xHain-hackspace/PlotterFeeder/src/play_sound/melodies_twisst.py

# taken from https://github.com/twisst/Music-for-Raspberry-Pi-Pico under GPL-3.0

# Songs to play with a buzzer connected to a Raspberry Pi Pico.
# Ported from https://github.com/robsoncouto/arduino-songs
# 
# Contents:
#
#  0. Star Trek intro
#  1. Silent Night
#  2. Pacman
#  3. Ode an die Freude, Beethoven's Symphony No. 9
#  4. Star Wars theme
#  5. Wiegenlied (Brahms' Lullaby)
#  6. Theme A from Tetris (Korobeiniki)
#  7. Happy Birthday
#  8. Darth Vader theme (Star Wars)
#  9. Nokia Ringtone
# 10. Mii Channel theme
# 11. Minuet in G - Petzold
# 12. Badinerie - Johann Sebastian Bach
# 13. Für Elise - Ludwig van Beethoven
# 14. Cantina Band (Star wars)
# 15. Song of storms (The Legend of Zelda, Ocarina of Time)
# 16. The Lion Sleeps Tonight
# 17. The Lick
# 18. Canon in D - Pachelbel
# 19. At Doom's Gate
# 20. Pink Panther theme
# 21. Hedwig's theme (Harry Potter)
# 22. Jigglypuff's Song (Pokémon)
# 23. We Wish You a Merry Christmas
# 24. Keyboard cat
# 25. Game of Thrones
# 26. Greensleeves
# 27. Green Hill Zone (Sonic the Hedgehog)
# 28. The Legend of Zelda theme
# 29. Baby Elephant Walk
# 30. Bloody Tears (Castlevania II)
# 31. O Pulo da Gaita (Auto da Compadecida)
# 32. Vampire Killer (Castlevania)
# 33. Never Gonna Give You Up - Rick Astley
# 34. Take on me - A-ha
# 35. Prince Igor - Polovtsian Dances, Borodin
# 36. Zelda's Lullaby - The Legend of Zelda, Ocarina of Time
# 37. Super Mario Bros theme, by Koji Kondo
# 38. Asa branca - Luiz Gonzaga
# 39. The Godfather theme
# 40. Professor Layton's theme


melody = []
notes = []


# 
# Star Trek intro
# Score available at https://musescore.com/user/10768291/scores/4594271
# 
notes = ['Star Trek intro', 80, 'NOTE_D4', '-8', 'NOTE_G4', '16', 'NOTE_C5', '-4', 'NOTE_B4', '8', 'NOTE_G4', '-16', 'NOTE_E4', '-16', 'NOTE_A4', '-16', 'NOTE_D5', '2']
melody.append(notes)
# 
# Silent Night
# Score available at https://musescore.com/marcsabatella/scores/3123436
# 
notes = ['Silent Night', 140, 'NOTE_G4', '-4', 'NOTE_A4', '8', 'NOTE_G4', '4', 'NOTE_E4', '-2', 'NOTE_G4', '-4', 'NOTE_A4', '8', 'NOTE_G4', '4', 'NOTE_E4', '-2', 'NOTE_D5', '2', 'NOTE_D5', '4', 'NOTE_B4', '-2', 'NOTE_C5', '2', 'NOTE_C5', '4', 'NOTE_G4', '-2', 'NOTE_A4', '2', 'NOTE_A4', '4', 'NOTE_C5', '-4', 'NOTE_B4', '8', 'NOTE_A4', '4', 'NOTE_G4', '-4', 'NOTE_A4', '8', 'NOTE_G4', '4', 'NOTE_E4', '-2', 'NOTE_A4', '2', 'NOTE_A4', '4', 'NOTE_C5', '-4', 'NOTE_B4', '8', 'NOTE_A4', '4', 'NOTE_G4', '-4', 'NOTE_A4', '8', 'NOTE_G4', '4', 'NOTE_E4', '-2', 'NOTE_D5', '2', 'NOTE_D5', '4', 'NOTE_F5', '-4', 'NOTE_D5', '8', 'NOTE_B4', '4', 'NOTE_C5', '-2', 'NOTE_E5', '-2', 'NOTE_C5', '4', 'NOTE_G4', '4', 'NOTE_E4', '4', 'NOTE_G4', '-4', 'NOTE_F4', '8', 'NOTE_D4', '4', 'NOTE_C4', '-2', 'NOTE_C4', '-1']
melody.append(notes)
# 
# Pacman
# Score available at https://musescore.com/user/85429/scores/107109
notes = ['Pacman', 105, 'NOTE_B4', '16', 'NOTE_B5', '16', 'NOTE_FS5', '16', 'NOTE_DS5', '16', 'NOTE_B5', '32', 'NOTE_FS5', '-16', 'NOTE_DS5', '8', 'NOTE_C5', '16', 'NOTE_C6', '16', 'NOTE_G6', '16', 'NOTE_E6', '16', 'NOTE_C6', '32', 'NOTE_G6', '-16', 'NOTE_E6', '8', 'NOTE_B4', '16', 'NOTE_B5', '16', 'NOTE_FS5', '16', 'NOTE_DS5', '16', 'NOTE_B5', '32', 'NOTE_FS5', '-16', 'NOTE_DS5', '8', 'NOTE_DS5', '32', 'NOTE_E5', '32', 'NOTE_F5', '32', 'NOTE_F5', '32', 'NOTE_FS5', '32', 'NOTE_G5', '32', 'NOTE_G5', '32', 'NOTE_GS5', '32', 'NOTE_A5', '16', 'NOTE_B5', '8']
melody.append(notes)
# 
# Ode an die Freude - Beethoven's Symphony No. 9 
# 
notes = ['Ode an die Freude', 114, 'NOTE_E4', '4', 'NOTE_E4', '4', 'NOTE_F4', '4', 'NOTE_G4', '4', 'NOTE_G4', '4', 'NOTE_F4', '4', 'NOTE_E4', '4', 'NOTE_D4', '4', 'NOTE_C4', '4', 'NOTE_C4', '4', 'NOTE_D4', '4', 'NOTE_E4', '4', 'NOTE_E4', '-4', 'NOTE_D4', '8', 'NOTE_D4', '2', 'NOTE_E4', '4', 'NOTE_E4', '4', 'NOTE_F4', '4', 'NOTE_G4', '4', 'NOTE_G4', '4', 'NOTE_F4', '4', 'NOTE_E4', '4', 'NOTE_D4', '4', 'NOTE_C4', '4', 'NOTE_C4', '4', 'NOTE_D4', '4', 'NOTE_E4', '4', 'NOTE_D4', '-4', 'NOTE_C4', '8', 'NOTE_C4', '2', 'NOTE_D4', '4', 'NOTE_D4', '4', 'NOTE_E4', '4', 'NOTE_C4', '4', 'NOTE_D4', '4', 'NOTE_E4', '8', 'NOTE_F4', '8', 'NOTE_E4', '4', 'NOTE_C4', '4', 'NOTE_D4', '4', 'NOTE_E4', '8', 'NOTE_F4', '8', 'NOTE_E4', '4', 'NOTE_D4', '4', 'NOTE_C4', '4', 'NOTE_D4', '4', 'NOTE_G3', '2', 'NOTE_E4', '4', 'NOTE_E4', '4', 'NOTE_F4', '4', 'NOTE_G4', '4', 'NOTE_G4', '4', 'NOTE_F4', '4', 'NOTE_E4', '4', 'NOTE_D4', '4', 'NOTE_C4', '4', 'NOTE_C4', '4', 'NOTE_D4', '4', 'NOTE_E4', '4', 'NOTE_D4', '-4', 'NOTE_C4', '8', 'NOTE_C4', '2']
melody.append(notes)
# 
# Star Wars theme
#
notes = ['Star Wars theme', 108, 'NOTE_AS4', '8', 'NOTE_AS4', '8', 'NOTE_AS4', '8', 'NOTE_F5', '2', 'NOTE_C6', '2', 'NOTE_AS5', '8', 'NOTE_A5', '8', 'NOTE_G5', '8', 'NOTE_F6', '2', 'NOTE_C6', '4', 'NOTE_AS5', '8', 'NOTE_A5', '8', 'NOTE_G5', '8', 'NOTE_F6', '2', 'NOTE_C6', '4', 'NOTE_AS5', '8', 'NOTE_A5', '8', 'NOTE_AS5', '8', 'NOTE_G5', '2', 'NOTE_C5', '8', 'NOTE_C5', '8', 'NOTE_C5', '8', 'NOTE_F5', '2', 'NOTE_C6', '2', 'NOTE_AS5', '8', 'NOTE_A5', '8', 'NOTE_G5', '8', 'NOTE_F6', '2', 'NOTE_C6', '4', 'NOTE_AS5', '8', 'NOTE_A5', '8', 'NOTE_G5', '8', 'NOTE_F6', '2', 'NOTE_C6', '4', 'NOTE_AS5', '8', 'NOTE_A5', '8', 'NOTE_AS5', '8', 'NOTE_G5', '2', 'NOTE_C5', '-8', 'NOTE_C5', '16', 'NOTE_D5', '-4', 'NOTE_D5', '8', 'NOTE_AS5', '8', 'NOTE_A5', '8', 'NOTE_G5', '8', 'NOTE_F5', '8', 'NOTE_F5', '8', 'NOTE_G5', '8', 'NOTE_A5', '8', 'NOTE_G5', '4', 'NOTE_D5', '8', 'NOTE_E5', '4', 'NOTE_C5', '-8', 'NOTE_C5', '16', 'NOTE_D5', '-4', 'NOTE_D5', '8', 'NOTE_AS5', '8', 'NOTE_A5', '8', 'NOTE_G5', '8', 'NOTE_F5', '8', 'NOTE_C6', '-8', 'NOTE_G5', '16', 'NOTE_G5', '2', 'REST', '8', 'NOTE_C5', '8', 'NOTE_D5', '-4', 'NOTE_D5', '8', 'NOTE_AS5', '8', 'NOTE_A5', '8', 'NOTE_G5', '8', 'NOTE_F5', '8', 'NOTE_F5', '8', 'NOTE_G5', '8', 'NOTE_A5', '8', 'NOTE_G5', '4', 'NOTE_D5', '8', 'NOTE_E5', '4', 'NOTE_C6', '-8', 'NOTE_C6', '16', 'NOTE_F6', '4', 'NOTE_DS6', '8', 'NOTE_CS6', '4', 'NOTE_C6', '8', 'NOTE_AS5', '4', 'NOTE_GS5', '8', 'NOTE_G5', '4', 'NOTE_F5', '8', 'NOTE_C6', '1']
melody.append(notes)
# 
# Wiegenlied (Brahms' Lullaby)
# Score available at https://www.flutetunes.com/tunes.php?id=54
# 
notes = ['Wiegenlied (Brahms\' Lullaby)', 76, 'NOTE_G4', '4', 'NOTE_G4', '4', 'NOTE_AS4', '-4', 'NOTE_G4', '8', 'NOTE_G4', '4', 'NOTE_AS4', '4', 'REST', '4', 'NOTE_G4', '8', 'NOTE_AS4', '8', 'NOTE_DS5', '4', 'NOTE_D5', '-4', 'NOTE_C5', '8', 'NOTE_C5', '4', 'NOTE_AS4', '4', 'NOTE_F4', '8', 'NOTE_G4', '8', 'NOTE_GS4', '4', 'NOTE_F4', '4', 'NOTE_F4', '8', 'NOTE_G4', '8', 'NOTE_GS4', '4', 'REST', '4', 'NOTE_F4', '8', 'NOTE_GS4', '8', 'NOTE_D5', '8', 'NOTE_C5', '8', 'NOTE_AS4', '4', 'NOTE_D5', '4', 'NOTE_DS5', '4', 'REST', '4', 'NOTE_DS4', '8', 'NOTE_DS4', '8', 'NOTE_DS5', '2', 'NOTE_C5', '8', 'NOTE_GS4', '8', 'NOTE_AS4', '2', 'NOTE_G4', '8', 'NOTE_DS4', '8', 'NOTE_GS4', '4', 'NOTE_AS4', '4', 'NOTE_C5', '4', 'NOTE_AS4', '2', 'NOTE_DS4', '8', 'NOTE_DS4', '8', 'NOTE_DS5', '2', 'NOTE_C5', '8', 'NOTE_GS4', '8', 'NOTE_AS4', '2', 'NOTE_G4', '8', 'NOTE_DS4', '8', 'NOTE_AS4', '4', 'NOTE_G4', '4', 'NOTE_DS4', '4', 'NOTE_DS4', '2']
melody.append(notes)
# 
# Theme A from Tetris (Korobeiniki)
# Based on the arrangement at https://www.flutetunes.com/tunes.php?id=192
# 
notes = ['Theme A from Tetris (Korobeiniki)', 144, 'NOTE_E5', '4', 'NOTE_B4', '8', 'NOTE_C5', '8', 'NOTE_D5', '4', 'NOTE_C5', '8', 'NOTE_B4', '8', 'NOTE_A4', '4', 'NOTE_A4', '8', 'NOTE_C5', '8', 'NOTE_E5', '4', 'NOTE_D5', '8', 'NOTE_C5', '8', 'NOTE_B4', '-4', 'NOTE_C5', '8', 'NOTE_D5', '4', 'NOTE_E5', '4', 'NOTE_C5', '4', 'NOTE_A4', '4', 'NOTE_A4', '8', 'NOTE_A4', '4', 'NOTE_B4', '8', 'NOTE_C5', '8', 'NOTE_D5', '-4', 'NOTE_F5', '8', 'NOTE_A5', '4', 'NOTE_G5', '8', 'NOTE_F5', '8', 'NOTE_E5', '-4', 'NOTE_C5', '8', 'NOTE_E5', '4', 'NOTE_D5', '8', 'NOTE_C5', '8', 'NOTE_B4', '4', 'NOTE_B4', '8', 'NOTE_C5', '8', 'NOTE_D5', '4', 'NOTE_E5', '4', 'NOTE_C5', '4', 'NOTE_A4', '4', 'NOTE_A4', '4', 'REST', '4', 'NOTE_E5', '4', 'NOTE_B4', '8', 'NOTE_C5', '8', 'NOTE_D5', '4', 'NOTE_C5', '8', 'NOTE_B4', '8', 'NOTE_A4', '4', 'NOTE_A4', '8', 'NOTE_C5', '8', 'NOTE_E5', '4', 'NOTE_D5', '8', 'NOTE_C5', '8', 'NOTE_B4', '-4', 'NOTE_C5', '8', 'NOTE_D5', '4', 'NOTE_E5', '4', 'NOTE_C5', '4', 'NOTE_A4', '4', 'NOTE_A4', '8', 'NOTE_A4', '4', 'NOTE_B4', '8', 'NOTE_C5', '8', 'NOTE_D5', '-4', 'NOTE_F5', '8', 'NOTE_A5', '4', 'NOTE_G5', '8', 'NOTE_F5', '8', 'NOTE_E5', '-4', 'NOTE_C5', '8', 'NOTE_E5', '4', 'NOTE_D5', '8', 'NOTE_C5', '8', 'NOTE_B4', '4', 'NOTE_B4', '8', 'NOTE_C5', '8', 'NOTE_D5', '4', 'NOTE_E5', '4', 'NOTE_C5', '4', 'NOTE_A4', '4', 'NOTE_A4', '4', 'REST', '4', 'NOTE_E5', '2', 'NOTE_C5', '2', 'NOTE_D5', '2', 'NOTE_B4', '2', 'NOTE_C5', '2', 'NOTE_A4', '2', 'NOTE_GS4', '2', 'NOTE_B4', '4', 'REST', '8', 'NOTE_E5', '2', 'NOTE_C5', '2', 'NOTE_D5', '2', 'NOTE_B4', '2', 'NOTE_C5', '4', 'NOTE_E5', '4', 'NOTE_A5', '2', 'NOTE_GS5', '2']
melody.append(notes)
# 
# Happy Birthday
# Score available at https://musescore.com/user/8221/scores/26906
# 
notes = ['Happy Birthday', 140, 'NOTE_C4', '4', 'NOTE_C4', '8', 'NOTE_D4', '-4', 'NOTE_C4', '-4', 'NOTE_F4', '-4', 'NOTE_E4', '-2', 'NOTE_C4', '4', 'NOTE_C4', '8', 'NOTE_D4', '-4', 'NOTE_C4', '-4', 'NOTE_G4', '-4', 'NOTE_F4', '-2', 'NOTE_C4', '4', 'NOTE_C4', '8', 'NOTE_C5', '-4', 'NOTE_A4', '-4', 'NOTE_F4', '-4', 'NOTE_E4', '-4', 'NOTE_D4', '-4', 'NOTE_AS4', '4', 'NOTE_AS4', '8', 'NOTE_A4', '-4', 'NOTE_F4', '-4', 'NOTE_G4', '-4', 'NOTE_F4', '-2']
melody.append(notes)
# 
# Darth Vader theme (Imperial March) - Star wars
# Score available at https://musescore.com/user/202909/scores/1141521
# The tenor saxophone part was used
# 
notes = ['Dart Vader theme', 120, 'NOTE_A4', '-4', 'NOTE_A4', '-4', 'NOTE_A4', '16', 'NOTE_A4', '16', 'NOTE_A4', '16', 'NOTE_A4', '16', 'NOTE_F4', '8', 'REST', '8', 'NOTE_A4', '-4', 'NOTE_A4', '-4', 'NOTE_A4', '16', 'NOTE_A4', '16', 'NOTE_A4', '16', 'NOTE_A4', '16', 'NOTE_F4', '8', 'REST', '8', 'NOTE_A4', '4', 'NOTE_A4', '4', 'NOTE_A4', '4', 'NOTE_F4', '-8', 'NOTE_C5', '16', 'NOTE_A4', '4', 'NOTE_F4', '-8', 'NOTE_C5', '16', 'NOTE_A4', '2', 'NOTE_E5', '4', 'NOTE_E5', '4', 'NOTE_E5', '4', 'NOTE_F5', '-8', 'NOTE_C5', '16', 'NOTE_A4', '4', 'NOTE_F4', '-8', 'NOTE_C5', '16', 'NOTE_A4', '2', 'NOTE_A5', '4', 'NOTE_A4', '-8', 'NOTE_A4', '16', 'NOTE_A5', '4', 'NOTE_GS5', '-8', 'NOTE_G5', '16', 'NOTE_DS5', '16', 'NOTE_D5', '16', 'NOTE_DS5', '8', 'REST', '8', 'NOTE_A4', '8', 'NOTE_DS5', '4', 'NOTE_D5', '-8', 'NOTE_CS5', '16', 'NOTE_C5', '16', 'NOTE_B4', '16', 'NOTE_C5', '16', 'REST', '8', 'NOTE_F4', '8', 'NOTE_GS4', '4', 'NOTE_F4', '-8', 'NOTE_A4', '-16', 'NOTE_C5', '4', 'NOTE_A4', '-8', 'NOTE_C5', '16', 'NOTE_E5', '2', 'NOTE_A5', '4', 'NOTE_A4', '-8', 'NOTE_A4', '16', 'NOTE_A5', '4', 'NOTE_GS5', '-8', 'NOTE_G5', '16', 'NOTE_DS5', '16', 'NOTE_D5', '16', 'NOTE_DS5', '8', 'REST', '8', 'NOTE_A4', '8', 'NOTE_DS5', '4', 'NOTE_D5', '-8', 'NOTE_CS5', '16', 'NOTE_C5', '16', 'NOTE_B4', '16', 'NOTE_C5', '16', 'REST', '8', 'NOTE_F4', '8', 'NOTE_GS4', '4', 'NOTE_F4', '-8', 'NOTE_A4', '-16', 'NOTE_A4', '4', 'NOTE_F4', '-8', 'NOTE_C5', '16', 'NOTE_A4', '2']
melody.append(notes)
# 
# Nokia Ringtone
# Score available at https://musescore.com/user/29944637/scores/5266155
# 
notes = ['Nokia Ringtone', 180, 'NOTE_E5', '8', 'NOTE_D5', '8', 'NOTE_FS4', '4', 'NOTE_GS4', '4', 'NOTE_CS5', '8', 'NOTE_B4', '8', 'NOTE_D4', '4', 'NOTE_E4', '4', 'NOTE_B4', '8', 'NOTE_A4', '8', 'NOTE_CS4', '4', 'NOTE_E4', '4', 'NOTE_A4', '2']
melody.append(notes)
# 
# Mii Channel theme
# Score available at https://musescore.com/user/16403456/scores/4984153
# 
notes = ['Mii Channel theme', 114, 'NOTE_FS4', '8', 'REST', '8', 'NOTE_A4', '8', 'NOTE_CS5', '8', 'REST', '8', 'NOTE_A4', '8', 'REST', '8', 'NOTE_FS4', '8', 'NOTE_D4', '8', 'NOTE_D4', '8', 'NOTE_D4', '8', 'REST', '8', 'REST', '4', 'REST', '8', 'NOTE_CS4', '8', 'NOTE_D4', '8', 'NOTE_FS4', '8', 'NOTE_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
melody.append(notes)
# 
# Minuet in G - Petzold
# Score available at https://musescore.com/user/3402766/scores/1456391
notes = ['Minuet in G - Petzold', 140, 'NOTE_D5', '4', 'NOTE_G4', '8', 'NOTE_A4', '8', 'NOTE_B4', '8', 'NOTE_C5', '8', 'NOTE_D5', '4', 'NOTE_G4', '4', 'NOTE_G4', '4', 'NOTE_E5', '4', 'NOTE_C5', '8', 'NOTE_D5', '8', 'NOTE_E5', '8', 'NOTE_FS5', '8', 'NOTE_G5', '4', 'NOTE_G4', '4', 'NOTE_G4', '4', 'NOT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
melody.append(notes)
#
# Badinerie - Johann Sebastian Bach
notes = ['Badinerie - Johann Sebastian Bach', 120, 'NOTE_B5', '-8', 'NOTE_D6', '16', 'NOTE_B5', '16', 'NOTE_FS5', '-8', 'NOTE_B5', '16', 'NOTE_FS5', '16', 'NOTE_D5', '-8', 'NOTE_FS5', '16', 'NOTE_D5', '16', 'NOTE_B4', '4', 'NOTE_F4', '16', 'NOTE_B4', '16', 'NOTE_D5', '16', 'NOTE_B4', '16', 'NOTE_CS5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
melody.append(notes)
# 
# Für Elise - Ludwig van Beethoven
# Score available at https://musescore.com/user/28149610/scores/5281944
# 
notes = ['Für Elise - Ludwig van Beethoven', 80, 'NOTE_E5', '16', 'NOTE_DS5', '16', 'NOTE_E5', '16', 'NOTE_DS5', '16', 'NOTE_E5', '16', 'NOTE_B4', '16', 'NOTE_D5', '16', 'NOTE_C5', '16', 'NOTE_A4', '-8', 'NOTE_C4', '16', 'NOTE_E4', '16', 'NOTE_A4', '16', 'NOTE_B4', '-8', 'NOTE_E4', '16', 'NOTE_GS4', '16', 'NOTE_B4', '16', 'NOTE_C5', '8', 'REST', '16', 'NOTE_E4', '16', 'NOTE_E5', '16', 'NOTE_DS5', '16', 'NOTE_E5', '16', 'NOTE_DS5', '16', 'NOTE_E5', '16', 'NOTE_B4', '16', 'NOTE_D5', '16', 'NOTE_C5', '16', 'NOTE_A4', '-8', 'NOTE_C4', '16', 'NOTE_E4', '16', 'NOTE_A4', '16', 'NOTE_B4', '-8', 'NOTE_E4', '16', 'NOTE_C5', '16', 'NOTE_B4', '16', 'NOTE_A4', '4', 'REST', '8', 'NOTE_E5', '16', 'NOTE_DS5', '16', 'NOTE_E5', '16', 'NOTE_DS5', '16', 'NOTE_E5', '16', 'NOTE_B4', '16', 'NOTE_D5', '16', 'NOTE_C5', '16', 'NOTE_A4', '-8', 'NOTE_C4', '16', 'NOTE_E4', '16', 'NOTE_A4', '16', 'NOTE_B4', '-8', 'NOTE_E4', '16', 'NOTE_GS4', '16', 'NOTE_B4', '16', 'NOTE_C5', '8', 'REST', '16', 'NOTE_E4', '16', 'NOTE_E5', '16', 'NOTE_DS5', '16', 'NOTE_E5', '16', 'NOTE_DS5', '16', 'NOTE_E5', '16', 'NOTE_B4', '16', 'NOTE_D5', '16', 'NOTE_C5', '16', 'NOTE_A4', '-8', 'NOTE_C4', '16', 'NOTE_E4', '16', 'NOTE_A4', '16', 'NOTE_B4', '-8', 'NOTE_E4', '16', 'NOTE_C5', '16', 'NOTE_B4', '16', 'NOTE_A4', '8', 'REST', '16', 'NOTE_B4', '16', 'NOTE_C5', '16', 'NOTE_D5', '16', 'NOTE_E5', '-8', 'NOTE_G4', '16', 'NOTE_F5', '16', 'NOTE_E5', '16', 'NOTE_D5', '-8', 'NOTE_F4', '16', 'NOTE_E5', '16', 'NOTE_D5', '16', 'NOTE_C5', '-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
6', 'NOTE_B4', '16', 'NOTE_D5', '16', 'NOTE_C5', '16', 'NOTE_A4', '-8', 'NOTE_C4', '16', 'NOTE_E4', '16', 'NOTE_A4', '16', 'NOTE_B4', '-8', 'NOTE_E4', '16', 'NOTE_C5', '16', 'NOTE_B4', '16', 'NOTE_A4', '-8', 'REST', '-8', 'REST', '-8', 'NOTE_G4', '16', 'NOTE_F5', '16', 'NOTE_E5', '16', 'NOTE_D5', '4', 'REST', '8', 'REST', '-8', 'NOTE_E4', '16', 'NOTE_D5', '16', 'NOTE_C5', '16', 'NOTE_B4', '-8', 'NOTE_E4', '16', 'NOTE_E5', '8', 'NOTE_E5', '8', 'NOTE_E6', '-8', 'NOTE_DS5', '16', 'NOTE_E5', '16', 'REST', '16', 'REST', '16', 'NOTE_DS5', '16', 'NOTE_E5', '16', 'NOTE_DS5', '16', 'NOTE_E5', '16', 'NOTE_DS5', '16', 'NOTE_E5', '16', 'NOTE_B4', '16', 'NOTE_D5', '16', 'NOTE_C5', '16', 'NOTE_A4', '-8', 'NOTE_C4', '16', 'NOTE_E4', '16', 'NOTE_A4', '16', 'NOTE_B4', '-8', 'NOTE_E4', '16', 'NOTE_GS4', '16', 'NOTE_B4', '16', 'NOTE_C5', '8', 'REST', '16', 'NOTE_E4', '16', 'NOTE_E5', '16', 'NOTE_DS5', '16', 'NOTE_E5', '16', 'NOTE_DS5', '16', 'NOTE_E5', '16', 'NOTE_B4', '16', 'NOTE_D5', '16', 'NOTE_C5', '16', 'NOTE_A4', '-8', 'NOTE_C4', '16', 'NOTE_E4', '16', 'NOTE_A4', '16', 'NOTE_B4', '-8', 'NOTE_E4', '16', 'NOTE_C5', '16', 'NOTE_B4', '16', 'NOTE_A4', '-4']
melody.append(notes)
# 
# Cantina Band (Star wars)
# Score available at https://musescore.com/user/6795541/scores/1606876
notes = ['Cantina Band (Star wars)', 140, 'NOTE_B4', '-4', 'NOTE_E5', '-4', 'NOTE_B4', '-4', 'NOTE_E5', '-4', 'NOTE_B4', '8', 'NOTE_E5', '-4', 'NOTE_B4', '8', 'REST', '8', 'NOTE_AS4', '8', 'NOTE_B4', '8', 'NOTE_B4', '8', 'NOTE_AS4', '8', 'NOTE_B4', '8', 'NOTE_A4', '8', 'REST', '8', 'NOTE_GS4', '8', 'NOTE_A4', '8', 'NOTE_G4', '8', 'NOTE_G4', '4', 'NOTE_E4', '-2', 'NOTE_B4', '-4', 'NOTE_E5', '-4', 'NOTE_B4', '-4', 'NOTE_E5', '-4', 'NOTE_B4', '8', 'NOTE_E5', '-4', 'NOTE_B4', '8', 'REST', '8', 'NOTE_AS4', '8', 'NOTE_B4', '8', 'NOTE_A4', '-4', 'NOTE_A4', '-4', 'NOTE_GS4', '8', 'NOTE_A4', '-4', 'NOTE_D5', '8', 'NOTE_C5', '-4', 'NOTE_B4', '-4', 'NOTE_A4', '-4', 'NOTE_B4', '-4', 'NOTE_E5', '-4', 'NOTE_B4', '-4', 'NOTE_E5', '-4', 'NOTE_B4', '8', 'NOTE_E5', '-4', 'NOTE_B4', '8', 'REST', '8', 'NOTE_AS4', '8', 'NOTE_B4', '8', 'NOTE_D5', '4', 'NOTE_D5', '-4', 'NOTE_B4', '8', 'NOTE_A4', '-4', 'NOTE_G4', '-4', 'NOTE_E4', '-2', 'NOTE_E4', '2', 'NOTE_G4', '2', 'NOTE_B4', '2', 'NOTE_D5', '2', 'NOTE_F5', '-4', 'NOTE_E5', '-4', 'NOTE_AS4', '8', 'NOTE_AS4', '8', 'NOTE_B4', '4', 'NOTE_G4', '4']
melody.append(notes)
# 
# Song of storms (The Legend of Zelda, Ocarina of Time)
# Score available at https://musescore.com/user/4957541/scores/1545401
# 
notes = ['Song of storms (The Legend of Zelda, Ocarina of Time)', 108, 'NOTE_D4', '4', 'NOTE_A4', '4', 'NOTE_A4', '4', 'REST', '8', 'NOTE_E4', '8', 'NOTE_B4', '2', 'NOTE_F4', '4', 'NOTE_C5', '4', 'NOTE_C5', '4', 'REST', '8', 'NOTE_E4', '8', 'NOTE_B4', '2', 'NOTE_D4', '4', 'NOTE_A4', '4', 'NOTE_A4', '4', 'REST', '8', 'NOTE_E4', '8', 'NOTE_B4', '2', 'NOTE_F4', '4', 'NOTE_C5', '4', 'NOTE_C5', '4', 'REST', '8', 'NOTE_E4', '8', 'NOTE_B4', '2', 'NOTE_D4', '8', 'NOTE_F4', '8', 'NOTE_D5', '2', 'NOTE_D4', '8', 'NOTE_F4', '8', 'NOTE_D5', '2', 'NOTE_E5', '-4', 'NOTE_F5', '8', 'NOTE_E5', '8', 'NOTE_E5', '8', 'NOTE_E5', '8', 'NOTE_C5', '8', 'NOTE_A4', '2', 'NOTE_A4', '4', 'NOTE_D4', '4', 'NOTE_F4', '8', 'NOTE_G4', '8', 'NOTE_A4', '-2', 'NOTE_A4', '4', 'NOTE_D4', '4', 'NOTE_F4', '8', 'NOTE_G4', '8', 'NOTE_E4', '-2', 'NOTE_D4', '8', 'NOTE_F4', '8', 'NOTE_D5', '2', 'NOTE_D4', '8', 'NOTE_F4', '8', 'NOTE_D5', '2', 'NOTE_E5', '-4', 'NOTE_F5', '8', 'NOTE_E5', '8', 'NOTE_E5', '8', 'NOTE_E5', '8', 'NOTE_C5', '8', 'NOTE_A4', '2', 'NOTE_A4', '4', 'NOTE_D4', '4', 'NOTE_F4', '8', 'NOTE_G4', '8', 'NOTE_A4', '2', 'NOTE_A4', '4', 'NOTE_D4', '1']
melody.append(notes)
# 
# The Lion Sleeps Tonight
# Score available at https://musescore.com/user/18545446/scores/5061407
# 
notes = ['The Lion Sleeps Tonight', 122, 'NOTE_F4', '4', 'NOTE_G4', '4', 'NOTE_A4', '8', 'NOTE_G4', '4', 'NOTE_A4', '8', 'NOTE_AS4', '4', 'NOTE_A4', '4', 'NOTE_G4', '8', 'NOTE_F4', '4', 'NOTE_G4', '8', 'NOTE_A4', '4', 'NOTE_C4', '8', 'NOTE_C4', '4', 'NOTE_C4', '8', 'NOTE_C4', '4', 'NOTE_C4', '1', 'N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
melody.append(notes)
# 
# The Lick
notes = ['The Lick', 108, 'NOTE_D4', '8', 'NOTE_E4', '8', 'NOTE_F4', '8', 'NOTE_G4', '8', 'NOTE_E4', '4', 'NOTE_C4', '8', 'NOTE_D4', '1']
melody.append(notes)
# 
# Canon in D - Pachelbel
# Score available at https://musescore.com/user/4710311/scores/1975521
#
notes = ['Canon in D - Pachelbel', 100, 'NOTE_FS4', '2', 'NOTE_E4', '2', 'NOTE_D4', '2', 'NOTE_CS4', '2', 'NOTE_B3', '2', 'NOTE_A3', '2', 'NOTE_B3', '2', 'NOTE_CS4', '2', 'NOTE_FS4', '2', 'NOTE_E4', '2', 'NOTE_D4', '2', 'NOTE_CS4', '2', 'NOTE_B3', '2', 'NOTE_A3', '2', 'NOTE_B3', '2', 'NOTE_CS4', '2', 'NOTE_D4', '2', 'NOTE_CS4', '2', 'NOTE_B3', '2', 'NOTE_A3', '2', 'NOTE_G3', '2', 'NOTE_FS3', '2', 'NOTE_G3', '2', 'NOTE_A3', '2', 'NOTE_D4', '4', 'NOTE_FS4', '8', 'NOTE_G4', '8', 'NOTE_A4', '4', 'NOTE_FS4', '8', 'NOTE_G4', '8', 'NOTE_A4', '4', 'NOTE_B3', '8', 'NOTE_CS4', '8', 'NOTE_D4', '8', 'NOTE_E4', '8', 'NOTE_FS4', '8', 'NOTE_G4', '8', 'NOTE_FS4', '4', 'NOTE_D4', '8', 'NOTE_E4', '8', 'NOTE_FS4', '4', 'NOTE_FS3', '8', 'NOTE_G3', '8', 'NOTE_A3', '8', 'NOTE_G3', '8', 'NOTE_FS3', '8', 'NOTE_G3', '8', 'NOTE_A3', '2', 'NOTE_G3', '4', 'NOTE_B3', '8', 'NOTE_A3', '8', 'NOTE_G3', '4', 'NOTE_FS3', '8', 'NOTE_E3', '8', 'NOTE_FS3', '4', 'NOTE_D3', '8', 'NOTE_E3', '8', 'NOTE_FS3', '8', 'NOTE_G3', '8', 'NOTE_A3', '8', 'NOTE_B3', '8', 'NOTE_G3', '4', 'NOTE_B3', '8', 'NOTE_A3', '8', 'NOTE_B3', '4', 'NOTE_CS4', '8', 'NOTE_D4', '8', 'NOTE_A3', '8', 'NOTE_B3', '8', 'NOTE_CS4', '8', 'NOTE_D4', '8', 'NOTE_E4', '8', 'NOTE_FS4', '8', 'NOTE_G4', '8', 'NOTE_A4', '2', 'NOTE_A4', '4', 'NOTE_FS4', '8', 'NOTE_G4', '8', 'NOTE_A4', '4', 'NOTE_FS4', '8', 'NOTE_G4', '8', 'NOTE_A4', '8', 'NOTE_A3', '8', 'NOTE_B3', '8', 'NOTE_CS4', '8', 'NOTE_D4', '8', 'NOTE_E4', '8', 'NOTE_FS4', '8', 'NOTE_G4', '8', 'NOTE_FS4', '4', 'NOTE_D4', '8', 'NOTE_E4', '8', 'NOTE_FS4', '8', 'NOTE_CS4', '8', 'NOTE_A3', '8', 'NOTE_A3', '8', 'NOTE_CS4', '4', 'NOTE_B3', '4', 'NOTE_D4', '8', 'NOTE_CS4', '8', 'NOTE_B3', '4', 'NOTE_A3', '8', 'NOTE_G3', '8', 'NOTE_A3', '4', 'NOTE_D3', '8', 'NOTE_E3', '8', 'NOTE_FS3', '8', 'NOTE_G3', '8', 'NOTE_A3', '8', 'NOTE_B3', '4', 'NOTE_G3', '4', 'NOTE_B3', '8', 'NOTE_A3', '8', 'NOTE_B3', '4', 'NOTE_CS4', '8', 'NOTE_D4', '8', 'NOTE_A3', '8', 'NOTE_B3', '8', 'NOTE_CS4', '8', 'NOTE_D4', '8', 'NOTE_E4', '8', 'NOTE_FS4', '8', 'NOTE_G4', '8', 'NOTE_A4', '2']
melody.append(notes)
# 
# At Doom's Gate (E1M1)
# Score available at https://musescore.com/pieridot/doom
# 
notes = ['At Doom\'s Gate (E1M1)', 225, 'NOTE_E2', '8', 'NOTE_E2', '8', 'NOTE_E3', '8', 'NOTE_E2', '8', 'NOTE_E2', '8', 'NOTE_D3', '8', 'NOTE_E2', '8', 'NOTE_E2', '8', 'NOTE_C3', '8', 'NOTE_E2', '8', 'NOTE_E2', '8', 'NOTE_AS2', '8', 'NOTE_E2', '8', 'NOTE_E2', '8', 'NOTE_B2', '8', 'NOTE_C3', '8', 'NOTE_E2', '8', 'NOTE_E2', '8', 'NOTE_E3', '8', 'NOTE_E2', '8', 'NOTE_E2', '8', 'NOTE_D3', '8', 'NOTE_E2', '8', 'NOTE_E2', '8', 'NOTE_C3', '8', 'NOTE_E2', '8', 'NOTE_E2', '8', 'NOTE_AS2', '-2', 'NOTE_E2', '8', 'NOTE_E2', '8', 'NOTE_E3', '8', 'NOTE_E2', '8', 'NOTE_E2', '8', 'NOTE_D3', '8', 'NOTE_E2', '8', 'NOTE_E2', '8', 'NOTE_C3', '8', 'NOTE_E2', '8', 'NOTE_E2', '8', 'NOTE_AS2', '8', 'NOTE_E2', '8', 'NOTE_E2', '8', 'NOTE_B2', '8', 'NOTE_C3', '8', 'NOTE_E2', '8', 'NOTE_E2', '8', 'NOTE_E3', '8', 'NOTE_E2', '8', 'NOTE_E2', '8', 'NOTE_D3', '8', 'NOTE_E2', '8', 'NOTE_E2', '8', 'NOTE_C3', '8', 'NOTE_E2', '8', 'NOTE_E2', '8', 'NOTE_AS2', '-2', 'NOTE_E2', '8', 'NOTE_E2', '8', 'NOTE_E3', '8', 'NOTE_E2', '8', 'NOTE_E2', '8', 'NOTE_D3', '8', 'NOTE_E2', '8', 'NOTE_E2', '8', 'NOTE_C3', '8', 'NOTE_E2', '8', 'NOTE_E2', '8', 'NOTE_AS2', '8', 'NOTE_E2', '8', 'NOTE_E2', '8', 'NOTE_B2', '8', 'NOTE_C3', '8', 'NOTE_E2', '8', 'NOTE_E2', '8', 'NOTE_E3', '8', 'NOTE_E2', '8', 'NOTE_E2', '8', 'NOTE_D3', '8', 'NOTE_E2', '8', 'NOTE_E2', '8', 'NOTE_C3', '8', 'NOTE_E2', '8', 'NOTE_E2', '8', 'NOTE_AS2', '-2', 'NOTE_E2', '8', 'NOTE_E2', '8', 'NOTE_E3', '8', 'NOTE_E2', '8', 'NOTE_E2', '8', 'NOTE_D3', '8', 'NOTE_E2', 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
melody.append(notes)
# 
# Pink Panther theme
# Score available at https://musescore.com/benedictsong/the-pink-panther
# 
notes = ['Pink Panther theme', 120, 'REST', '2', 'REST', '4', 'REST', '8', 'NOTE_DS4', '8', 'NOTE_E4', '-4', 'REST', '8', 'NOTE_FS4', '8', 'NOTE_G4', '-4', 'REST', '8', 'NOTE_DS4', '8', 'NOTE_E4', '-8', 'NOTE_FS4', '8', 'NOTE_G4', '-8', 'NOTE_C5', '8', 'NOTE_B4', '-8', 'NOTE_E4', '8', 'NOTE_G4', '-8', 'NOTE_B4', '8', 'NOTE_AS4', '2', 'NOTE_A4', '-16', 'NOTE_G4', '-16', 'NOTE_E4', '-16', 'NOTE_D4', '-16', 'NOTE_E4', '2', 'REST', '4', 'REST', '8', 'NOTE_DS4', '4', 'NOTE_E4', '-4', 'REST', '8', 'NOTE_FS4', '8', 'NOTE_G4', '-4', 'REST', '8', 'NOTE_DS4', '8', 'NOTE_E4', '-8', 'NOTE_FS4', '8', 'NOTE_G4', '-8', 'NOTE_C5', '8', 'NOTE_B4', '-8', 'NOTE_G4', '8', 'NOTE_B4', '-8', 'NOTE_E5', '8', 'NOTE_DS5', '1', 'NOTE_D5', '2', 'REST', '4', 'REST', '8', 'NOTE_DS4', '8', 'NOTE_E4', '-4', 'REST', '8', 'NOTE_FS4', '8', 'NOTE_G4', '-4', 'REST', '8', 'NOTE_DS4', '8', 'NOTE_E4', '-8', 'NOTE_FS4', '8', 'NOTE_G4', '-8', 'NOTE_C5', '8', 'NOTE_B4', '-8', 'NOTE_E4', '8', 'NOTE_G4', '-8', 'NOTE_B4', '8', 'NOTE_AS4', '2', 'NOTE_A4', '-16', 'NOTE_G4', '-16', 'NOTE_E4', '-16', 'NOTE_D4', '-16', 'NOTE_E4', '-4', 'REST', '4', 'REST', '4', 'NOTE_E5', '-8', 'NOTE_D5', '8', 'NOTE_B4', '-8', 'NOTE_A4', '8', 'NOTE_G4', '-8', 'NOTE_E4', '-8', 'NOTE_AS4', '16', 'NOTE_A4', '-8', 'NOTE_AS4', '16', 'NOTE_A4', '-8', 'NOTE_AS4', '16', 'NOTE_A4', '-8', 'NOTE_AS4', '16', 'NOTE_A4', '-8', 'NOTE_G4', '-16', 'NOTE_E4', '-16', 'NOTE_D4', '-16', 'NOTE_E4', '16', 'NOTE_E4', '16', 'NOTE_E4', '2']
melody.append(notes)
# 
# 
# Hedwig's theme (Harry Potter)
# Socre from https://musescore.com/user/3811306/scores/4906610
# 
notes = ['Hedwig\'s theme (Harry Potter)', 144, 'REST', '2', 'NOTE_D4', '4', 'NOTE_G4', '-4', 'NOTE_AS4', '8', 'NOTE_A4', '4', 'NOTE_G4', '2', 'NOTE_D5', '4', 'NOTE_C5', '-2', 'NOTE_A4', '-2', 'NOTE_G4', '-4', 'NOTE_AS4', '8', 'NOTE_A4', '4', 'NOTE_F4', '2', 'NOTE_GS4', '4', 'NOTE_D4', '-1', 'NOTE_D4', '4', 'NOTE_G4', '-4', 'NOTE_AS4', '8', 'NOTE_A4', '4', 'NOTE_G4', '2', 'NOTE_D5', '4', 'NOTE_F5', '2', 'NOTE_E5', '4', 'NOTE_DS5', '2', 'NOTE_B4', '4', 'NOTE_DS5', '-4', 'NOTE_D5', '8', 'NOTE_CS5', '4', 'NOTE_CS4', '2', 'NOTE_B4', '4', 'NOTE_G4', '-1', 'NOTE_AS4', '4', 'NOTE_D5', '2', 'NOTE_AS4', '4', 'NOTE_D5', '2', 'NOTE_AS4', '4', 'NOTE_DS5', '2', 'NOTE_D5', '4', 'NOTE_CS5', '2', 'NOTE_A4', '4', 'NOTE_AS4', '-4', 'NOTE_D5', '8', 'NOTE_CS5', '4', 'NOTE_CS4', '2', 'NOTE_D4', '4', 'NOTE_D5', '-1', 'REST', '4', 'NOTE_AS4', '4', 'NOTE_D5', '2', 'NOTE_AS4', '4', 'NOTE_D5', '2', 'NOTE_AS4', '4', 'NOTE_F5', '2', 'NOTE_E5', '4', 'NOTE_DS5', '2', 'NOTE_B4', '4', 'NOTE_DS5', '-4', 'NOTE_D5', '8', 'NOTE_CS5', '4', 'NOTE_CS4', '2', 'NOTE_AS4', '4', 'NOTE_G4', '-1']
melody.append(notes)
# 
# Jigglypuff's Song
# Score available at https://musescore.com/user/28109683/scores/5044153
# 
notes = ['Jigglypuff\'s Song', 85, 'NOTE_D5', '-4', 'NOTE_A5', '8', 'NOTE_FS5', '8', 'NOTE_D5', '8', 'NOTE_E5', '-4', 'NOTE_FS5', '8', 'NOTE_G5', '4', 'NOTE_FS5', '-4', 'NOTE_E5', '8', 'NOTE_FS5', '4', 'NOTE_D5', '-2', 'NOTE_D5', '-4', 'NOTE_A5', '8', 'NOTE_FS5', '8', 'NOTE_D5', '8', 'NOTE_E5', '-4', 'NOTE_FS5', '8', 'NOTE_G5', '4', 'NOTE_FS5', '-1', 'NOTE_D5', '-4', 'NOTE_A5', '8', 'NOTE_FS5', '8', 'NOTE_D5', '8', 'NOTE_E5', '-4', 'NOTE_FS5', '8', 'NOTE_G5', '4', 'NOTE_FS5', '-4', 'NOTE_E5', '8', 'NOTE_FS5', '4', 'NOTE_D5', '-2', 'NOTE_D5', '-4', 'NOTE_A5', '8', 'NOTE_FS5', '8', 'NOTE_D5', '8', 'NOTE_E5', '-4', 'NOTE_FS5', '8', 'NOTE_G5', '4', 'NOTE_FS5', '-1']
melody.append(notes)
# 
# We Wish You a Merry Christmas
# Score available at https://musescore.com/user/6208766/scores/1497501
# 
notes = ['We Wish You a Merry Christmas', 140, 'NOTE_C5', '4', 'NOTE_F5', '4', 'NOTE_F5', '8', 'NOTE_G5', '8', 'NOTE_F5', '8', 'NOTE_E5', '8', 'NOTE_D5', '4', 'NOTE_D5', '4', 'NOTE_D5', '4', 'NOTE_G5', '4', 'NOTE_G5', '8', 'NOTE_A5', '8', 'NOTE_G5', '8', 'NOTE_F5', '8', 'NOTE_E5', '4', 'NOTE_C5', '4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
melody.append(notes)
# 
# Keyboard cat
# Score available at https://musescore.com/user/142788/scores/147371
# 
notes = ['Keyboard cat', 160, 'REST', '1', 'REST', '1', 'NOTE_C4', '4', 'NOTE_E4', '4', 'NOTE_G4', '4', 'NOTE_E4', '4', 'NOTE_C4', '4', 'NOTE_E4', '8', 'NOTE_G4', '-4', 'NOTE_E4', '4', 'NOTE_A3', '4', 'NOTE_C4', '4', 'NOTE_E4', '4', 'NOTE_C4', '4', 'NOTE_A3', '4', 'NOTE_C4', '8', 'NOTE_E4', '-4', 'NOTE_C4', '4', 'NOTE_G3', '4', 'NOTE_B3', '4', 'NOTE_D4', '4', 'NOTE_B3', '4', 'NOTE_G3', '4', 'NOTE_B3', '8', 'NOTE_D4', '-4', 'NOTE_B3', '4', 'NOTE_G3', '4', 'NOTE_G3', '8', 'NOTE_G3', '-4', 'NOTE_G3', '8', 'NOTE_G3', '4', 'NOTE_G3', '4', 'NOTE_G3', '4', 'NOTE_G3', '8', 'NOTE_G3', '4', 'NOTE_C4', '4', 'NOTE_E4', '4', 'NOTE_G4', '4', 'NOTE_E4', '4', 'NOTE_C4', '4', 'NOTE_E4', '8', 'NOTE_G4', '-4', 'NOTE_E4', '4', 'NOTE_A3', '4', 'NOTE_C4', '4', 'NOTE_E4', '4', 'NOTE_C4', '4', 'NOTE_A3', '4', 'NOTE_C4', '8', 'NOTE_E4', '-4', 'NOTE_C4', '4', 'NOTE_G3', '4', 'NOTE_B3', '4', 'NOTE_D4', '4', 'NOTE_B3', '4', 'NOTE_G3', '4', 'NOTE_B3', '8', 'NOTE_D4', '-4', 'NOTE_B3', '4', 'NOTE_G3', '-1']
melody.append(notes)
# 
# Game of Thrones
# Score available at https://musescore.com/user/8407786/scores/2156716
# 
notes = ['Game of Thrones', 85, 'NOTE_G4', '8', 'NOTE_C4', '8', 'NOTE_DS4', '16', 'NOTE_F4', '16', 'NOTE_G4', '8', 'NOTE_C4', '8', 'NOTE_DS4', '16', 'NOTE_F4', '16', 'NOTE_G4', '8', 'NOTE_C4', '8', 'NOTE_DS4', '16', 'NOTE_F4', '16', 'NOTE_G4', '8', 'NOTE_C4', '8', 'NOTE_DS4', '16', 'NOTE_F4', '16', 'NOTE_G4', '8', 'NOTE_C4', '8', 'NOTE_E4', '16', 'NOTE_F4', '16', 'NOTE_G4', '8', 'NOTE_C4', '8', 'NOTE_E4', '16', 'NOTE_F4', '16', 'NOTE_G4', '8', 'NOTE_C4', '8', 'NOTE_E4', '16', 'NOTE_F4', '16', 'NOTE_G4', '8', 'NOTE_C4', '8', 'NOTE_E4', '16', 'NOTE_F4', '16', 'NOTE_G4', '-4', 'NOTE_C4', '-4', 'NOTE_DS4', '16', 'NOTE_F4', '16', 'NOTE_G4', '4', 'NOTE_C4', '4', 'NOTE_DS4', '16', 'NOTE_F4', '16', 'NOTE_D4', '-1', 'NOTE_F4', '-4', 'NOTE_AS3', '-4', 'NOTE_DS4', '16', 'NOTE_D4', '16', 'NOTE_F4', '4', 'NOTE_AS3', '-4', 'NOTE_DS4', '16', 'NOTE_D4', '16', 'NOTE_C4', '-1', 'NOTE_G4', '-4', 'NOTE_C4', '-4', 'NOTE_DS4', '16', 'NOTE_F4', '16', 'NOTE_G4', '4', 'NOTE_C4', '4', 'NOTE_DS4', '16', 'NOTE_F4', '16', 'NOTE_D4', '-1', 'NOTE_F4', '-4', 'NOTE_AS3', '-4', 'NOTE_DS4', '16', 'NOTE_D4', '16', 'NOTE_F4', '4', 'NOTE_AS3', '-4', 'NOTE_DS4', '16', 'NOTE_D4', '16', 'NOTE_C4', '-1', 'NOTE_G4', '-4', 'NOTE_C4', '-4', 'NOTE_DS4', '16', 'NOTE_F4', '16', 'NOTE_G4', '4', 'NOTE_C4', '4', 'NOTE_DS4', '16', 'NOTE_F4', '16', 'NOTE_D4', '-2', 'NOTE_F4', '-4', 'NOTE_AS3', '-4', 'NOTE_D4', '-8', 'NOTE_DS4', '-8', 'NOTE_D4', '-8', 'NOTE_AS3', '-8', 'NOTE_C4', '-1', 'NOTE_C5', '-2', 'NOTE_AS4', '-2', 'NOTE_C4', '-2', 'NOTE_G4', '-2', 'NOTE_DS4', '-2', 'NOTE_DS4', '-4', 'NOTE_F4', '-4', 'NOTE_G4', '-1', 'NOTE_C5', '-2', 'NOTE_AS4', '-2', 'NOTE_C4', '-2', 'NOTE_G4', '-2', 'NOTE_DS4', '-2', 'NOTE_DS4', '-4', 'NOTE_D4', '-4', 'NOTE_C5', '8', 'NOTE_G4', '8', 'NOTE_GS4', '16', 'NOTE_AS4', '16', 'NOTE_C5', '8', 'NOTE_G4', '8', 'NOTE_GS4', '16', 'NOTE_AS4', '16', 'NOTE_C5', '8', 'NOTE_G4', '8', 'NOTE_GS4', '16', 'NOTE_AS4', '16', 'NOTE_C5', '8', 'NOTE_G4', '8', 'NOTE_GS4', '16', 'NOTE_AS4', '16', 'REST', '4', 'NOTE_GS5', '16', 'NOTE_AS5', '16', 'NOTE_C6', '8', 'NOTE_G5', '8', 'NOTE_GS5', '16', 'NOTE_AS5', '16', 'NOTE_C6', '8', 'NOTE_G5', '16', 'NOTE_GS5', '16', 'NOTE_AS5', '16', 'NOTE_C6', '8', 'NOTE_G5', '8', 'NOTE_GS5', '16', 'NOTE_AS5', '16']
melody.append(notes)
# 
# Greensleeves
# Score available at https://musescore.com/user/168402/scores/1396946
# 
notes = ['Greensleeves', 70, 'NOTE_G4', '8', 'NOTE_AS4', '4', 'NOTE_C5', '8', 'NOTE_D5', '-8', 'NOTE_DS5', '16', 'NOTE_D5', '8', 'NOTE_C5', '4', 'NOTE_A4', '8', 'NOTE_F4', '-8', 'NOTE_G4', '16', 'NOTE_A4', '8', 'NOTE_AS4', '4', 'NOTE_G4', '8', 'NOTE_G4', '-8', 'NOTE_FS4', '16', 'NOTE_G4', '8', 'NOTE_A4', '4', 'NOTE_FS4', '8', 'NOTE_D4', '4', 'NOTE_G4', '8', 'NOTE_AS4', '4', 'NOTE_C5', '8', 'NOTE_D5', '-8', 'NOTE_DS5', '16', 'NOTE_D5', '8', 'NOTE_C5', '4', 'NOTE_A4', '8', 'NOTE_F4', '-8', 'NOTE_G4', '16', 'NOTE_A4', '8', 'NOTE_AS4', '-8', 'NOTE_A4', '16', 'NOTE_G4', '8', 'NOTE_FS4', '-8', 'NOTE_E4', '16', 'NOTE_FS4', '8', 'NOTE_G4', '-2', 'NOTE_F5', '2', 'NOTE_E5', '16', 'NOTE_D5', '8', 'NOTE_C5', '4', 'NOTE_A4', '8', 'NOTE_F4', '-8', 'NOTE_G4', '16', 'NOTE_A4', '8', 'NOTE_AS4', '4', 'NOTE_G4', '8', 'NOTE_G4', '-8', 'NOTE_FS4', '16', 'NOTE_G4', '8', 'NOTE_A4', '4', 'NOTE_FS4', '8', 'NOTE_D4', '04', 'NOTE_F5', '2', 'NOTE_E5', '16', 'NOTE_D5', '8', 'NOTE_C5', '4', 'NOTE_A4', '8', 'NOTE_F4', '-8', 'NOTE_G4', '16', 'NOTE_A4', '8', 'NOTE_AS4', '-8', 'NOTE_A4', '16', 'NOTE_G4', '8', 'NOTE_FS4', '-8', 'NOTE_E4', '16', 'NOTE_FS4', '8', 'NOTE_G4', '-2', 'NOTE_G4', '8', 'NOTE_AS4', '4', 'NOTE_C5', '8', 'NOTE_D5', '-8', 'NOTE_DS5', '16', 'NOTE_D5', '8', 'NOTE_C5', '4', 'NOTE_A4', '8', 'NOTE_F4', '-8', 'NOTE_G4', '16', 'NOTE_A4', '8', 'NOTE_AS4', '4', 'NOTE_G4', '8', 'NOTE_G4', '-8', 'NOTE_FS4', '16', 'NOTE_G4', '8', 'NOTE_A4', '4', 'NOTE_FS4', '8', 'NOTE_D4', '4', 'NOTE_G4', '8', 'NOTE_AS4', '4', 'NOTE_C5', '8', 'NOTE_D5', '-8', 'NOTE_DS5', '16', 'NOTE_D5', '8', 'NOTE_C5', '4', 'NOTE_A4', '8', 'NOTE_F4', '-8', 'NOTE_G4', '16', 'NOTE_A4', '8', 'NOTE_AS4', '-8', 'NOTE_A4', '16', 'NOTE_G4', '8', 'NOTE_FS4', '-8', 'NOTE_E4', '16', 'NOTE_FS4', '8', 'NOTE_G4', '-2', 'NOTE_F5', '2', 'NOTE_E5', '16', 'NOTE_D5', '8', 'NOTE_C5', '4', 'NOTE_A4', '8', 'NOTE_F4', '-8', 'NOTE_G4', '16', 'NOTE_A4', '8', 'NOTE_AS4', '4', 'NOTE_G4', '8', 'NOTE_G4', '-8', 'NOTE_FS4', '16', 'NOTE_G4', '8', 'NOTE_A4', '4', 'NOTE_FS4', '8', 'NOTE_D4', '04', 'NOTE_F5', '2', 'NOTE_E5', '16', 'NOTE_D5', '8', 'NOTE_C5', '4', 'NOTE_A4', '8', 'NOTE_F4', '-8', 'NOTE_G4', '16', 'NOTE_A4', '8', 'NOTE_AS4', '-8', 'NOTE_A4', '16', 'NOTE_G4', '8', 'NOTE_FS4', '-8', 'NOTE_E4', '16', 'NOTE_FS4', '8', 'NOTE_G4', '-2']
melody.append(notes)
# 
# Green Hill Zone - Sonic the Hedgehog
# Score available at https://musescore.com/user/248346/scores/461661
# 
notes = ['Green Hill Zone - Sonic the Hedgehog', 140, 'REST', '2', 'NOTE_D5', '8', 'NOTE_B4', '4', 'NOTE_D5', '8', 'NOTE_CS5', '4', 'NOTE_D5', '8', 'NOTE_CS5', '4', 'NOTE_A4', '2', 'REST', '8', 'NOTE_A4', '8', 'NOTE_FS5', '8', 'NOTE_E5', '4', 'NOTE_D5', '8', 'NOTE_CS5', '4', 'NOTE_D5', '8', 'NOTE_CS5', '4', 'NOTE_A4', '2', 'REST', '4', 'NOTE_D5', '8', 'NOTE_B4', '4', 'NOTE_D5', '8', 'NOTE_CS5', '4', 'NOTE_D5', '8', 'NOTE_CS5', '4', 'NOTE_A4', '2', 'REST', '8', 'NOTE_B4', '8', 'NOTE_B4', '8', 'NOTE_G4', '4', 'NOTE_B4', '8', 'NOTE_A4', '4', 'NOTE_B4', '8', 'NOTE_A4', '4', 'NOTE_D4', '2', 'REST', '4', 'NOTE_D5', '8', 'NOTE_B4', '4', 'NOTE_D5', '8', 'NOTE_CS5', '4', 'NOTE_D5', '8', 'NOTE_CS5', '4', 'NOTE_A4', '2', 'REST', '8', 'NOTE_A4', '8', 'NOTE_FS5', '8', 'NOTE_E5', '4', 'NOTE_D5', '8', 'NOTE_CS5', '4', 'NOTE_D5', '8', 'NOTE_CS5', '4', 'NOTE_A4', '2', 'REST', '4', 'NOTE_D5', '8', 'NOTE_B4', '4', 'NOTE_D5', '8', 'NOTE_CS5', '4', 'NOTE_D5', '8', 'NOTE_CS5', '4', 'NOTE_A4', '2', 'REST', '8', 'NOTE_B4', '8', 'NOTE_B4', '8', 'NOTE_G4', '4', 'NOTE_B4', '8', 'NOTE_A4', '4', 'NOTE_B4', '8', 'NOTE_A4', '4', 'NOTE_D4', '8', 'NOTE_D4', '8', 'NOTE_FS4', '8', 'NOTE_E4', '-1', 'REST', '8', 'NOTE_D4', '8', 'NOTE_E4', '8', 'NOTE_FS4', '-1', 'REST', '8', 'NOTE_D4', '8', 'NOTE_D4', '8', 'NOTE_FS4', '8', 'NOTE_F4', '-1', 'REST', '8', 'NOTE_D4', '8', 'NOTE_F4', '8', 'NOTE_E4', '-1', 'REST', '2', 'NOTE_D5', '8', 'NOTE_B4', '4', 'NOTE_D5', '8', 'NOTE_CS5', '4', 'NOTE_D5', '8', 'NOTE_CS5', '4', 'NOTE_A4', '2', 'REST', '8', 'NOTE_A4', '8', 'NOTE_FS5', '8', 'NOTE_E5', '4', 'NOTE_D5', '8', 'NOTE_CS5', '4', 'NOTE_D5', '8', 'NOTE_CS5', '4', 'NOTE_A4', '2', 'REST', '4', 'NOTE_D5', '8', 'NOTE_B4', '4', 'NOTE_D5', '8', 'NOTE_CS5', '4', 'NOTE_D5', '8', 'NOTE_CS5', '4', 'NOTE_A4', '2', 'REST', '8', 'NOTE_B4', '8', 'NOTE_B4', '8', 'NOTE_G4', '4', 'NOTE_B4', '8', 'NOTE_A4', '4', 'NOTE_B4', '8', 'NOTE_A4', '4', 'NOTE_D4', '2', 'REST', '4', 'NOTE_D5', '8', 'NOTE_B4', '4', 'NOTE_D5', '8', 'NOTE_CS5', '4', 'NOTE_D5', '8', 'NOTE_CS5', '4', 'NOTE_A4', '2', 'REST', '8', 'NOTE_A4', '8', 'NOTE_FS5', '8', 'NOTE_E5', '4', 'NOTE_D5', '8', 'NOTE_CS5', '4', 'NOTE_D5', '8', 'NOTE_CS5', '4', 'NOTE_A4', '2', 'REST', '4', 'NOTE_D5', '8', 'NOTE_B4', '4', 'NOTE_D5', '8', 'NOTE_CS5', '4', 'NOTE_D5', '8', 'NOTE_CS5', '4', 'NOTE_A4', '2', 'REST', '8', 'NOTE_B4', '8', 'NOTE_B4', '8', 'NOTE_G4', '4', 'NOTE_B4', '8', 'NOTE_A4', '4', 'NOTE_B4', '8', 'NOTE_A4', '4', 'NOTE_D4', '8', 'NOTE_D4', '8', 'NOTE_FS4', '8', 'NOTE_E4', '-1', 'REST', '8', 'NOTE_D4', '8', 'NOTE_E4', '8', 'NOTE_FS4', '-1', 'REST', '8', 'NOTE_D4', '8', 'NOTE_D4', '8', 'NOTE_FS4', '8', 'NOTE_F4', '-1', 'REST', '8', 'NOTE_D4', '8', 'NOTE_F4', '8', 'NOTE_E4', '8', 'NOTE_E4', '-2', 'NOTE_A4', '8', 'NOTE_CS5', '8', 'NOTE_FS5', '8', 'NOTE_E5', '4', 'NOTE_D5', '8', 'NOTE_A5', '-4']
melody.append(notes)
# 
# The Legend of Zelda theme
# Based on the arrangement at https://www.flutetunes.com/tunes.php?id=169
# 
notes = ['The Legend of Zelda theme', 88, 'NOTE_AS4', '-2', 'NOTE_F4', '8', 'NOTE_F4', '8', 'NOTE_AS4', '8', 'NOTE_GS4', '16', 'NOTE_FS4', '16', 'NOTE_GS4', '-2', 'NOTE_AS4', '-2', 'NOTE_FS4', '8', 'NOTE_FS4', '8', 'NOTE_AS4', '8', 'NOTE_A4', '16', 'NOTE_G4', '16', 'NOTE_A4', '-2', 'REST', '1', 'NOTE_AS4', '4', 'NOTE_F4', '-4', 'NOTE_AS4', '8', 'NOTE_AS4', '16', 'NOTE_C5', '16', 'NOTE_D5', '16', 'NOTE_DS5', '16', 'NOTE_F5', '2', 'NOTE_F5', '8', 'NOTE_F5', '8', 'NOTE_F5', '8', 'NOTE_FS5', '16', 'NOTE_GS5', '16', 'NOTE_AS5', '-2', 'NOTE_AS5', '8', 'NOTE_AS5', '8', 'NOTE_GS5', '8', 'NOTE_FS5', '16', 'NOTE_GS5', '-8', 'NOTE_FS5', '16', 'NOTE_F5', '2', 'NOTE_F5', '4', 'NOTE_DS5', '-8', 'NOTE_F5', '16', 'NOTE_FS5', '2', 'NOTE_F5', '8', 'NOTE_DS5', '8', 'NOTE_CS5', '-8', 'NOTE_DS5', '16', 'NOTE_F5', '2', 'NOTE_DS5', '8', 'NOTE_CS5', '8', 'NOTE_C5', '-8', 'NOTE_D5', '16', 'NOTE_E5', '2', 'NOTE_G5', '8', 'NOTE_F5', '16', 'NOTE_F4', '16', 'NOTE_F4', '16', 'NOTE_F4', '16', 'NOTE_F4', '16', 'NOTE_F4', '16', 'NOTE_F4', '16', 'NOTE_F4', '16', 'NOTE_F4', '8', 'NOTE_F4', '16', 'NOTE_F4', '8', 'NOTE_AS4', '4', 'NOTE_F4', '-4', 'NOTE_AS4', '8', 'NOTE_AS4', '16', 'NOTE_C5', '16', 'NOTE_D5', '16', 'NOTE_DS5', '16', 'NOTE_F5', '2', 'NOTE_F5', '8', 'NOTE_F5', '8', 'NOTE_F5', '8', 'NOTE_FS5', '16', 'NOTE_GS5', '16', 'NOTE_AS5', '-2', 'NOTE_CS6', '4', 'NOTE_C6', '4', 'NOTE_A5', '2', 'NOTE_F5', '4', 'NOTE_FS5', '-2', 'NOTE_AS5', '4', 'NOTE_A5', '4', 'NOTE_F5', '2', 'NOTE_F5', '4', 'NOTE_FS5', '-2', 'NOTE_AS5', '4', 'NOTE_A5', '4', 'NOTE_F5', '2', 'NOTE_D5', '4', 'NOTE_DS5', '-2', 'NOTE_FS5', '4', 'NOTE_F5', '4', 'NOTE_CS5', '2', 'NOTE_AS4', '4', 'NOTE_C5', '-8', 'NOTE_D5', '16', 'NOTE_E5', '2', 'NOTE_G5', '8', 'NOTE_F5', '16', 'NOTE_F4', '16', 'NOTE_F4', '16', 'NOTE_F4', '16', 'NOTE_F4', '16', 'NOTE_F4', '16', 'NOTE_F4', '16', 'NOTE_F4', '16', 'NOTE_F4', '8', 'NOTE_F4', '16', 'NOTE_F4', '8']
melody.append(notes)
# 
# Baby Elephant Walk
# Score available at https://musescore.com/user/7965776/scores/1862611
# 
notes = ['Baby Elephant Walk', 132, 'NOTE_C4', '-8', 'NOTE_E4', '16', 'NOTE_G4', '8', 'NOTE_C5', '8', 'NOTE_E5', '8', 'NOTE_D5', '8', 'NOTE_C5', '8', 'NOTE_A4', '8', 'NOTE_FS4', '8', 'NOTE_G4', '8', 'REST', '4', 'REST', '2', 'NOTE_C4', '-8', 'NOTE_E4', '16', 'NOTE_G4', '8', 'NOTE_C5', '8', 'NOTE_E5', '8', 'NOTE_D5', '8', 'NOTE_C5', '8', 'NOTE_A4', '8', 'NOTE_G4', '-2', 'NOTE_A4', '8', 'NOTE_DS4', '1', 'NOTE_A4', '8', 'NOTE_E4', '8', 'NOTE_C4', '8', 'REST', '4', 'REST', '2', 'NOTE_C4', '-8', 'NOTE_E4', '16', 'NOTE_G4', '8', 'NOTE_C5', '8', 'NOTE_E5', '8', 'NOTE_D5', '8', 'NOTE_C5', '8', 'NOTE_A4', '8', 'NOTE_FS4', '8', 'NOTE_G4', '8', 'REST', '4', 'REST', '4', 'REST', '8', 'NOTE_G4', '8', 'NOTE_D5', '4', 'NOTE_D5', '4', 'NOTE_B4', '8', 'NOTE_G4', '8', 'REST', '8', 'NOTE_G4', '8', 'NOTE_C5', '4', 'NOTE_C5', '4', 'NOTE_AS4', '16', 'NOTE_C5', '16', 'NOTE_AS4', '16', 'NOTE_G4', '16', 'NOTE_F4', '8', 'NOTE_DS4', '8', 'NOTE_FS4', '4', 'NOTE_FS4', '4', 'NOTE_F4', '16', 'NOTE_G4', '16', 'NOTE_F4', '16', 'NOTE_DS4', '16', 'NOTE_C4', '8', 'NOTE_G4', '8', 'NOTE_AS4', '8', 'NOTE_C5', '8', 'REST', '4', 'REST', '2']
melody.append(notes)
# 
# Bloody Tears (Castlevania II)
# https://musescore.com/user/263171/scores/883296
# 
notes = ['Bloody Tears (Castlevania II)', 144, 'REST', '4', 'NOTE_G5', '4', 'NOTE_A5', '4', 'NOTE_AS5', '4', 'NOTE_A5', '4', 'NOTE_F5', '4', 'NOTE_A5', '4', 'NOTE_G5', '4', 'REST', '4', 'NOTE_G5', '4', 'NOTE_A5', '4', 'NOTE_AS5', '4', 'NOTE_C6', '4', 'NOTE_AS5', '4', 'NOTE_A5', '4', 'NOTE_G5', '4', 'REST', '4', 'NOTE_G5', '4', 'NOTE_A5', '4', 'NOTE_AS5', '4', 'NOTE_A5', '4', 'NOTE_F5', '4', 'NOTE_A5', '4', 'NOTE_G5', '4', 'NOTE_D6', '4', 'REST', '8', 'NOTE_C6', '8', 'REST', '4', 'NOTE_AS5', '4', 'NOTE_A5', '4', 'NOTE_AS5', '8', 'NOTE_C6', '8', 'NOTE_F6', '8', 'REST', '8', 'REST', '4', 'NOTE_G5', '16', 'NOTE_D5', '16', 'NOTE_D6', '16', 'NOTE_D5', '16', 'NOTE_C6', '16', 'NOTE_D5', '16', 'NOTE_AS5', '16', 'NOTE_D5', '16', 'NOTE_A5', '16', 'NOTE_D5', '16', 'NOTE_AS5', '16', 'NOTE_D5', '16', 'NOTE_A5', '16', 'NOTE_D5', '16', 'NOTE_G5', '16', 'NOTE_D5', '16', 'NOTE_A5', '16', 'NOTE_D5', '16', 'NOTE_AS5', '16', 'NOTE_D5', '16', 'NOTE_C6', '16', 'NOTE_D5', '16', 'NOTE_AS5', '16', 'NOTE_D5', '16', 'NOTE_A5', '16', 'NOTE_D5', '16', 'NOTE_F5', '16', 'NOTE_D5', '16', 'NOTE_A5', '16', 'NOTE_D5', '16', 'NOTE_G5', '16', 'NOTE_D5', '16', 'NOTE_G5', '16', 'NOTE_D5', '16', 'NOTE_D6', '16', 'NOTE_D5', '16', 'NOTE_C6', '16', 'NOTE_D5', '16', 'NOTE_AS5', '16', 'NOTE_D5', '16', 'NOTE_A5', '16', 'NOTE_D5', '16', 'NOTE_AS5', '16', 'NOTE_D5', '16', 'NOTE_A5', '16', 'NOTE_D5', '16', 'NOTE_AS5', '16', 'NOTE_D5', '16', 'NOTE_A5', '16', 'NOTE_D5', '16', 'NOTE_AS5', '16', 'NOTE_D5', '16', 'NOTE_C6', '16',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
OTE_AS5', '16', 'NOTE_DS5', '16', 'NOTE_GS5', '16', 'NOTE_DS5', '16', 'NOTE_GS5', '16', 'NOTE_DS5', '16', 'NOTE_DS6', '16', 'NOTE_DS5', '16', 'NOTE_CS6', '16', 'NOTE_DS5', '16', 'NOTE_B5', '16', 'NOTE_DS5', '16', 'NOTE_AS5', '16', 'NOTE_DS5', '16', 'NOTE_B5', '16', 'NOTE_DS5', '16', 'NOTE_AS5', '16', 'NOTE_DS5', '16', 'NOTE_GS5', '16', 'NOTE_DS5', '16', 'NOTE_AS5', '16', 'NOTE_DS5', '16', 'NOTE_B5', '16', 'NOTE_DS5', '16', 'NOTE_CS6', '16', 'NOTE_DS5', '16', 'NOTE_B5', '16', 'NOTE_DS5', '16', 'NOTE_AS5', '16', 'NOTE_DS5', '16', 'NOTE_FS5', '16', 'NOTE_DS5', '16', 'NOTE_AS5', '16', 'NOTE_DS5', '16', 'NOTE_GS5', '16', 'NOTE_DS5', '16', 'NOTE_GS5', '16', 'NOTE_DS5', '16', 'NOTE_DS6', '16', 'NOTE_DS5', '16', 'NOTE_CS6', '16', 'NOTE_DS5', '16', 'NOTE_B5', '16', 'NOTE_DS5', '16', 'NOTE_AS5', '16', 'NOTE_DS5', '16', 'NOTE_B5', '16', 'NOTE_DS5', '16', 'NOTE_AS5', '16', 'NOTE_DS5', '16', 'NOTE_GS5', '16', 'NOTE_DS5', '16', 'NOTE_AS5', '16', 'NOTE_DS5', '16', 'NOTE_B5', '16', 'NOTE_DS5', '16', 'NOTE_CS6', '16', 'NOTE_DS5', '16', 'NOTE_B5', '16', 'NOTE_DS5', '16', 'NOTE_AS5', '16', 'NOTE_DS5', '16', 'NOTE_FS5', '16', 'NOTE_DS5', '16', 'NOTE_AS5', '16', 'NOTE_DS5', '16', 'NOTE_GS5', '16', 'NOTE_DS5', '16', 'NOTE_CS6', '8', 'NOTE_FS6', '16', 'NOTE_DS6', '8', 'REST', '16', 'REST', '8', 'REST', '4', 'NOTE_CS6', '8', 'NOTE_B5', '8', 'NOTE_CS6', '-8', 'NOTE_FS6', '-8', 'NOTE_DS6', '-4', 'NOTE_CS6', '8', 'NOTE_B5', '8', 'NOTE_CS6', '8', 'NOTE_FS6', '16', 'NOTE_DS6', '8', 'REST', '16', 'REST', '8', 'REST', '4', 'NOTE_CS6', '8', 'NOTE_B5', '8', 'NOTE_E6', '-8', 'NOTE_F6', '-8', 'NOTE_DS6', '-8', 'REST', '16', 'NOTE_E6', '8', 'REST', '16', 'REST', '16', 'NOTE_CS6', '8', 'NOTE_FS6', '16', 'NOTE_DS6', '8', 'REST', '16', 'REST', '8', 'REST', '4', 'NOTE_CS6', '8', 'NOTE_B5', '8', 'NOTE_CS6', '-8', 'NOTE_FS6', '-8', 'NOTE_DS6', '-4', 'NOTE_CS6', '8', 'NOTE_B5', '8', 'NOTE_CS6', '8', 'NOTE_FS6', '16', 'NOTE_DS6', '8', 'REST', '16', 'REST', '8', 'REST', '4', 'NOTE_CS5', '8', 'NOTE_DS5', '8', 'NOTE_E5', '-8', 'NOTE_F5', '-8', 'NOTE_DS5', '8', 'NOTE_G5', '8', 'NOTE_GS5', '8', 'NOTE_AS5', '8', 'NOTE_AS5', '-8', 'NOTE_GS5', '-8', 'NOTE_AS5', '-8', 'NOTE_GS5', '-8', 'NOTE_AS5', '-8', 'NOTE_GS5', '-8', 'NOTE_B6', '8', 'NOTE_AS5', '8', 'NOTE_GS5', '8', 'NOTE_FS5', '8', 'NOTE_AS5', '-8', 'NOTE_GS6', '-8', 'NOTE_DS5', '8', 'NOTE_AS5', '-8', 'NOTE_GS6', '-8', 'NOTE_DS5', '8', 'NOTE_AS5', '-8', 'NOTE_GS6', '-8', 'NOTE_DS5', '8', 'NOTE_B5', '8', 'NOTE_CS6', '8', 'NOTE_AS5', '8', 'NOTE_B5', '8', 'NOTE_GS5', '8', 'REST', '8', 'REST', '16']
melody.append(notes)
# 
# O Pulo da Gaita (Auto da Compadecida)
# Score available at https://musescore.com/user/196039/scores/250206
# 
notes = ['O Pulo da Gaita (Auto da Compadecida)', 100, 'NOTE_C5', '4', 'NOTE_G4', '8', 'NOTE_AS4', '4', 'NOTE_A4', '8', 'NOTE_G4', '16', 'NOTE_C4', '8', 'NOTE_C4', '16', 'NOTE_G4', '16', 'NOTE_G4', '8', 'NOTE_G4', '16', 'NOTE_C5', '4', 'NOTE_G4', '8', 'NOTE_AS4', '4', 'NOTE_A4', '8', 'NOTE_G4', '2',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
melody.append(notes)
# 
# Vampire Killer (Castlevania)
# Score available at https://musescore.com/user/28972071/scores/5425616
#
notes = ['Vampire Killer (Castlevania)', 130, 'NOTE_E5', '16', 'NOTE_E5', '8', 'NOTE_D5', '16', 'REST', '16', 'NOTE_CS5', '-4', 'NOTE_E4', '8', 'NOTE_FS4', '16', 'NOTE_G4', '16', 'NOTE_A4', '16', 'NOTE_B4', '-8', 'NOTE_E4', '-8', 'NOTE_B4', '8', 'NOTE_A4', '16', 'NOTE_D5', '-4', 'NOTE_E5', '16', 'NO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
melody.append(notes)
# 
# Never Gonna Give You Up - Rick Astley
# Score available at https://musescore.com/chlorondria_5/never-gonna-give-you-up_alto-sax
# 
notes = ['Never Gonna Give You Up - Rick Astley', 114, 'NOTE_D5', '-4', 'NOTE_E5', '-4', 'NOTE_A4', '4', 'NOTE_E5', '-4', 'NOTE_FS5', '-4', 'NOTE_A5', '16', 'NOTE_G5', '16', 'NOTE_FS5', '8', 'NOTE_D5', '-4', 'NOTE_E5', '-4', 'NOTE_A4', '2', 'NOTE_A4', '16', 'NOTE_A4', '16', 'NOTE_B4', '16', 'NOTE_D5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
melody.append(notes)
# 
# Take on me - A-ha
# Score available at https://musescore.com/user/27103612/scores/4834399
# 
notes = ['Take on me - A-ha', 140, 'NOTE_FS5', '8', 'NOTE_FS5', '8', 'NOTE_D5', '8', 'NOTE_B4', '8', 'REST', '8', 'NOTE_B4', '8', 'REST', '8', 'NOTE_E5', '8', 'REST', '8', 'NOTE_E5', '8', 'REST', '8', 'NOTE_E5', '8', 'NOTE_GS5', '8', 'NOTE_GS5', '8', 'NOTE_A5', '8', 'NOTE_B5', '8', 'NOTE_A5', '8', 'NOTE_A5', '8', 'NOTE_A5', '8', 'NOTE_E5', '8', 'REST', '8', 'NOTE_D5', '8', 'REST', '8', 'NOTE_FS5', '8', 'REST', '8', 'NOTE_FS5', '8', 'REST', '8', 'NOTE_FS5', '8', 'NOTE_E5', '8', 'NOTE_E5', '8', 'NOTE_FS5', '8', 'NOTE_E5', '8', 'NOTE_FS5', '8', 'NOTE_FS5', '8', 'NOTE_D5', '8', 'NOTE_B4', '8', 'REST', '8', 'NOTE_B4', '8', 'REST', '8', 'NOTE_E5', '8', 'REST', '8', 'NOTE_E5', '8', 'REST', '8', 'NOTE_E5', '8', 'NOTE_GS5', '8', 'NOTE_GS5', '8', 'NOTE_A5', '8', 'NOTE_B5', '8', 'NOTE_A5', '8', 'NOTE_A5', '8', 'NOTE_A5', '8', 'NOTE_E5', '8', 'REST', '8', 'NOTE_D5', '8', 'REST', '8', 'NOTE_FS5', '8', 'REST', '8', 'NOTE_FS5', '8', 'REST', '8', 'NOTE_FS5', '8', 'NOTE_E5', '8', 'NOTE_E5', '8', 'NOTE_FS5', '8', 'NOTE_E5', '8', 'NOTE_FS5', '8', 'NOTE_FS5', '8', 'NOTE_D5', '8', 'NOTE_B4', '8', 'REST', '8', 'NOTE_B4', '8', 'REST', '8', 'NOTE_E5', '8', 'REST', '8', 'NOTE_E5', '8', 'REST', '8', 'NOTE_E5', '8', 'NOTE_GS5', '8', 'NOTE_GS5', '8', 'NOTE_A5', '8', 'NOTE_B5', '8', 'NOTE_A5', '8', 'NOTE_A5', '8', 'NOTE_A5', '8', 'NOTE_E5', '8', 'REST', '8', 'NOTE_D5', '8', 'REST', '8', 'NOTE_FS5', '8', 'REST', '8', 'NOTE_FS5', '8', 'REST', '8', 'NOTE_FS5', '8', 'NOTE_E5', '8', 'NOTE_E5', '8', 'NOTE_FS5', '8', 'NOTE_E5', '8']
melody.append(notes)
# 
# Prince Igor - Polovtsian Dances, Borodin
#
notes = ['Prince Igor - Polovtsian Dances, Borodin', 110, 'NOTE_G4', '4', 'NOTE_G4', '4', 'NOTE_D5', '-2', 'NOTE_C5', '8', 'NOTE_D5', '8', 'NOTE_AS4', '4', 'NOTE_A4', '8', 'NOTE_G4', '8', 'NOTE_A4', '8', 'NOTE_AS4', '8', 'NOTE_C5', '1', 'NOTE_D5', '4', 'NOTE_A4', '4', 'NOTE_G4', '8', 'NOTE_F4', '8', 'NOTE_D4', '4', 'NOTE_D4', '4', 'NOTE_G4', '-2', 'NOTE_A4', '4', 'NOTE_G4', '4', 'NOTE_F4', '8', 'NOTE_E4', '8', 'NOTE_F4', '4', 'NOTE_E4', '4', 'NOTE_D4', '1', 'NOTE_E4', '4', 'NOTE_F4', '4', 'NOTE_A4', '4', 'NOTE_G4', '4', 'NOTE_G4', '4', 'NOTE_AS4', '-2', 'NOTE_C5', '4', 'NOTE_AS4', '4', 'NOTE_A4', '8', 'NOTE_G4', '8', 'NOTE_A4', '4', 'NOTE_AS4', '4', 'NOTE_C5', '-2', 'NOTE_CS5', '4', 'NOTE_C5', '4', 'NOTE_A4', '4', 'NOTE_CS5', '4', 'NOTE_CS4', '4', 'NOTE_F5', '-2', 'NOTE_G5', '4', 'NOTE_F5', '4', 'NOTE_DS4', '8', 'NOTE_CS4', '8', 'NOTE_F5', '2', 'NOTE_C5', '-2', 'NOTE_AS4', '4', 'NOTE_C5', '4', 'NOTE_AS4', '8', 'NOTE_A4', '8', 'NOTE_G4', '4', 'NOTE_G4', '4', 'NOTE_AS4', '1', 'NOTE_C5', '4', 'NOTE_AS4', '4', 'NOTE_A4', '8', 'NOTE_G4', '8', 'NOTE_F4', '4', 'NOTE_G4', '4', 'NOTE_A4', '1', 'NOTE_AS4', '4', 'NOTE_A4', '4', 'NOTE_F4', '4', 'NOTE_G4', '4', 'NOTE_G4', '4', 'NOTE_D5', '-2', 'NOTE_C5', '4', 'NOTE_AS4', '4', 'NOTE_A4', '8', 'NOTE_G4', '8', 'NOTE_A4', '-1', 'NOTE_A4', '-1', 'REST', '2', 'NOTE_G4', '4', 'NOTE_G4', '4', 'NOTE_D5', '-2', 'NOTE_C5', '8', 'NOTE_D5', '8', 'NOTE_AS4', '4', 'NOTE_A4', '8', 'NOTE_G4', '8', 'NOTE_A4', '8', 'NOTE_AS4', '8', 'NOTE_C5', '1', 'NOTE_C5', '8', 'NOTE_D5', '8', 'NOTE_C5', '4', 'NOTE_AS4', '8', 'NOTE_A4', '8', 'NOTE_D4', '4', 'NOTE_D4', '4', 'NOTE_G4', '-2', 'NOTE_G4', '8', 'NOTE_A4', '8', 'NOTE_G4', '4', 'NOTE_F4', '8', 'NOTE_E4', '8', 'NOTE_F4', '8', 'NOTE_E4', '8', 'NOTE_D4', '-2', 'REST', '4', 'NOTE_C5', '8', 'NOTE_D5', '8', 'NOTE_C5', '4', 'NOTE_AS4', '8', 'NOTE_A4', '8', 'NOTE_G4', '4', 'NOTE_G4', '4', 'NOTE_B4', '-2', 'NOTE_C5', '4', 'NOTE_AS4', '4', 'NOTE_A4', '8', 'NOTE_G4', '8', 'NOTE_A4', '4', 'NOTE_G4', '4', 'NOTE_F4', '-1', 'REST', '4', 'NOTE_G4', '4', 'NOTE_G4', '4', 'NOTE_D5', '-2', 'NOTE_C5', '8', 'NOTE_D5', '8', 'NOTE_AS4', '4', 'NOTE_A4', '8', 'NOTE_G4', '8', 'NOTE_A4', '4', 'NOTE_G4', '4', 'NOTE_F4', '-2', 'NOTE_A4', '4', 'NOTE_G4', '4', 'NOTE_F4', '-2', 'NOTE_A4', '4', 'NOTE_G4', '4', 'NOTE_F4', '-1']
melody.append(notes)
# 
# Zelda's Lullaby (The Legend of Zelda, Ocarina of Time)
# Score available at https://musescore.com/user/12754451/scores/2762776
# 
notes = ['Zelda\'s Lullaby - The Legend of Zelda, Ocarina of Time', 108, 'NOTE_E4', '2', 'NOTE_G4', '4', 'NOTE_D4', '2', 'NOTE_C4', '8', 'NOTE_D4', '8', 'NOTE_E4', '2', 'NOTE_G4', '4', 'NOTE_D4', '-2', 'NOTE_E4', '2', 'NOTE_G4', '4', 'NOTE_D5', '2', 'NOTE_C5', '4', 'NOTE_G4', '2', 'NOTE_F4', '8', 'NOTE_E4', '8', 'NOTE_D4', '-2', 'NOTE_E4', '2', 'NOTE_G4', '4', 'NOTE_D4', '2', 'NOTE_C4', '8', 'NOTE_D4', '8', 'NOTE_E4', '2', 'NOTE_G4', '4', 'NOTE_D4', '-2', 'NOTE_E4', '2', 'NOTE_G4', '4', 'NOTE_D5', '2', 'NOTE_C5', '4', 'NOTE_G4', '2', 'NOTE_F4', '8', 'NOTE_E4', '8', 'NOTE_F4', '8', 'NOTE_E4', '8', 'NOTE_C4', '2', 'NOTE_F4', '2', 'NOTE_E4', '8', 'NOTE_D4', '8', 'NOTE_E4', '8', 'NOTE_D4', '8', 'NOTE_A3', '2', 'NOTE_G4', '2', 'NOTE_F4', '8', 'NOTE_E4', '8', 'NOTE_F4', '8', 'NOTE_E4', '8', 'NOTE_C4', '4', 'NOTE_F4', '4', 'NOTE_C5', '-2']
melody.append(notes)
# 
# Super Mario Bros theme, by Koji Kondo
# Score available at https://musescore.com/user/2123/scores/2145
# 
notes = ['Super Mario Bros theme, by Koji Kondo', 200, 'NOTE_E5', '8', 'NOTE_E5', '8', 'REST', '8', 'NOTE_E5', '8', 'REST', '8', 'NOTE_C5', '8', 'NOTE_E5', '8', 'NOTE_G5', '4', 'REST', '4', 'NOTE_G4', '8', 'REST', '4', 'NOTE_C5', '-4', 'NOTE_G4', '8', 'REST', '4', 'NOTE_E4', '-4', 'NOTE_A4', '4', 'N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
melody.append(notes)
# 
# Asa branca - Luiz Gonzaga
# Score available at https://musescore.com/user/190926/scores/181370
# 
notes = ['Asa branca - Luiz Gonzaga', 120, 'NOTE_G4', '8', 'NOTE_A4', '8', 'NOTE_B4', '4', 'NOTE_D5', '4', 'NOTE_D5', '4', 'NOTE_B4', '4', 'NOTE_C5', '4', 'NOTE_C5', '2', 'NOTE_G4', '8', 'NOTE_A4', '8', 'NOTE_B4', '4', 'NOTE_D5', '4', 'NOTE_D5', '4', 'NOTE_C5', '4', 'NOTE_B4', '2', 'REST', '8', 'NOTE_G4', '8', 'NOTE_G4', '8', 'NOTE_A4', '8', 'NOTE_B4', '4', 'NOTE_D5', '4', 'REST', '8', 'NOTE_D5', '8', 'NOTE_C5', '8', 'NOTE_B4', '8', 'NOTE_G4', '4', 'NOTE_C5', '4', 'REST', '8', 'NOTE_C5', '8', 'NOTE_B4', '8', 'NOTE_A4', '8', 'NOTE_A4', '4', 'NOTE_B4', '4', 'REST', '8', 'NOTE_B4', '8', 'NOTE_A4', '8', 'NOTE_G4', '8', 'NOTE_G4', '2', 'REST', '8', 'NOTE_G4', '8', 'NOTE_G4', '8', 'NOTE_A4', '8', 'NOTE_B4', '4', 'NOTE_D5', '4', 'REST', '8', 'NOTE_D5', '8', 'NOTE_C5', '8', 'NOTE_B4', '8', 'NOTE_G4', '4', 'NOTE_C5', '4', 'REST', '8', 'NOTE_C5', '8', 'NOTE_B4', '8', 'NOTE_A4', '8', 'NOTE_A4', '4', 'NOTE_B4', '4', 'REST', '8', 'NOTE_B4', '8', 'NOTE_A4', '8', 'NOTE_G4', '8', 'NOTE_G4', '4', 'NOTE_F5', '8', 'NOTE_D5', '8', 'NOTE_E5', '8', 'NOTE_C5', '8', 'NOTE_D5', '8', 'NOTE_B4', '8', 'NOTE_C5', '8', 'NOTE_A4', '8', 'NOTE_B4', '8', 'NOTE_G4', '8', 'NOTE_A4', '8', 'NOTE_G4', '8', 'NOTE_E4', '8', 'NOTE_G4', '8', 'NOTE_G4', '4', 'NOTE_F5', '8', 'NOTE_D5', '8', 'NOTE_E5', '8', 'NOTE_C5', '8', 'NOTE_D5', '8', 'NOTE_B4', '8', 'NOTE_C5', '8', 'NOTE_A4', '8', 'NOTE_B4', '8', 'NOTE_G4', '8', 'NOTE_A4', '8', 'NOTE_G4', '8', 'NOTE_E4', '8', 'NOTE_G4', '8', 'NOTE_G4', '-2', 'REST', '4']
melody.append(notes)
# 
# The Godfather theme
# Score available at https://musescore.com/user/35463/scores/55160
# 
notes = ['The Godfather theme', 80, 'REST', '4', 'REST', '8', 'REST', '8', 'REST', '8', 'NOTE_E4', '8', 'NOTE_A4', '8', 'NOTE_C5', '8', 'NOTE_B4', '8', 'NOTE_A4', '8', 'NOTE_C5', '8', 'NOTE_A4', '8', 'NOTE_B4', '8', 'NOTE_A4', '8', 'NOTE_F4', '8', 'NOTE_G4', '8', 'NOTE_E4', '2', 'NOTE_E4', '8', 'NOTE_A4', '8', 'NOTE_C5', '8', 'NOTE_B4', '8', 'NOTE_A4', '8', 'NOTE_C5', '8', 'NOTE_A4', '8', 'NOTE_C5', '8', 'NOTE_A4', '8', 'NOTE_E4', '8', 'NOTE_DS4', '8', 'NOTE_D4', '2', 'NOTE_D4', '8', 'NOTE_F4', '8', 'NOTE_GS4', '8', 'NOTE_B4', '2', 'NOTE_D4', '8', 'NOTE_F4', '8', 'NOTE_GS4', '8', 'NOTE_A4', '2', 'NOTE_C4', '8', 'NOTE_C4', '8', 'NOTE_G4', '8', 'NOTE_F4', '8', 'NOTE_E4', '8', 'NOTE_G4', '8', 'NOTE_F4', '8', 'NOTE_F4', '8', 'NOTE_E4', '8', 'NOTE_E4', '8', 'NOTE_GS4', '8', 'NOTE_A4', '2', 'REST', '8', 'NOTE_A4', '8', 'NOTE_A4', '8', 'NOTE_GS4', '8', 'NOTE_G4', '2', 'NOTE_B4', '8', 'NOTE_A4', '8', 'NOTE_F4', '8', 'NOTE_E4', '2', 'NOTE_E4', '8', 'NOTE_G4', '8', 'NOTE_E4', '8', 'NOTE_D4', '2', 'NOTE_D4', '8', 'NOTE_D4', '8', 'NOTE_F4', '8', 'NOTE_DS4', '8', 'NOTE_E4', '2', 'REST', '8', 'NOTE_E4', '8', 'NOTE_A4', '8', 'NOTE_C5', '8', 'NOTE_B4', '8', 'NOTE_A4', '8', 'NOTE_C5', '8', 'NOTE_A4', '8', 'NOTE_B4', '8', 'NOTE_A4', '8', 'NOTE_F4', '8', 'NOTE_G4', '8', 'NOTE_E4', '2', 'NOTE_E4', '8', 'NOTE_A4', '8', 'NOTE_C5', '8', 'NOTE_B4', '8', 'NOTE_A4', '8', 'NOTE_C5', '8', 'NOTE_A4', '8', 'NOTE_C5', '8', 'NOTE_A4', '8', 'NOTE_E4', '8', 'NOTE_DS4', '8', 'NOTE_D4', '2', 'NOTE_D4', '8', 'NOTE_F4', '8', 'NOTE_GS4', '8', 'NOTE_B4', '2', 'NOTE_D4', '8', 'NOTE_F4', '8', 'NOTE_GS4', '8', 'NOTE_A4', '2', 'NOTE_C4', '8', 'NOTE_C4', '8', 'NOTE_G4', '8', 'NOTE_F4', '8', 'NOTE_E4', '8', 'NOTE_G4', '8', 'NOTE_F4', '8', 'NOTE_F4', '8', 'NOTE_E4', '8', 'NOTE_E4', '8', 'NOTE_GS4', '8', 'NOTE_A4', '2', 'REST', '8', 'NOTE_A4', '8', 'NOTE_A4', '8', 'NOTE_GS4', '8', 'NOTE_G4', '2', 'NOTE_B4', '8', 'NOTE_A4', '8', 'NOTE_F4', '8', 'NOTE_E4', '2', 'NOTE_E4', '8', 'NOTE_G4', '8', 'NOTE_E4', '8', 'NOTE_D4', '2', 'NOTE_D4', '8', 'NOTE_D4', '8', 'NOTE_F4', '8', 'NOTE_DS4', '8', 'NOTE_E4', '2']
melody.append(notes)
# 
# Professor Layton's theme (Professor Layton and the Courious village)
# available at https://musescore.com/user/311366/scores/373161
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
